tfuru/ConnectedDoll2/shell/image/dist/acrylic_panel_preview.png

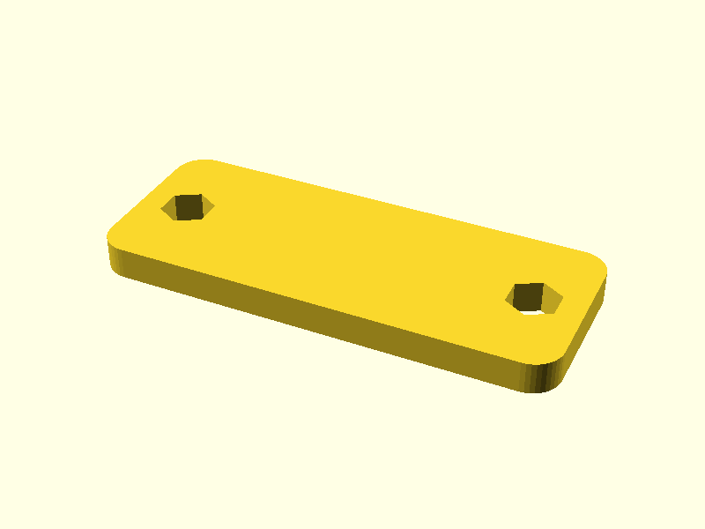
shell/image/dist/acrylic_panel_preview.png
