tfuru/ConnectedDoll2/shell/image/dist/battery_lid_preview.png

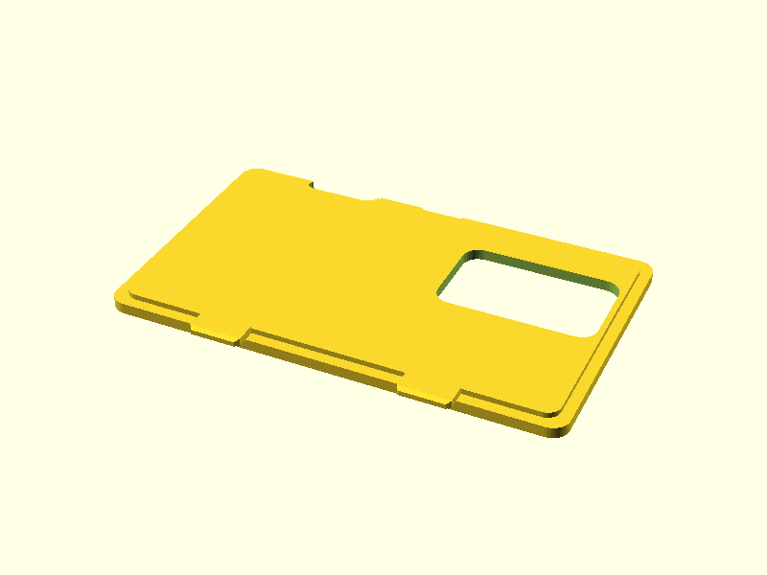
shell/image/dist/battery_lid_preview.png
