tfuru/ConnectedDoll2/shell/image/dist/battery_lid_tab_zoom.png

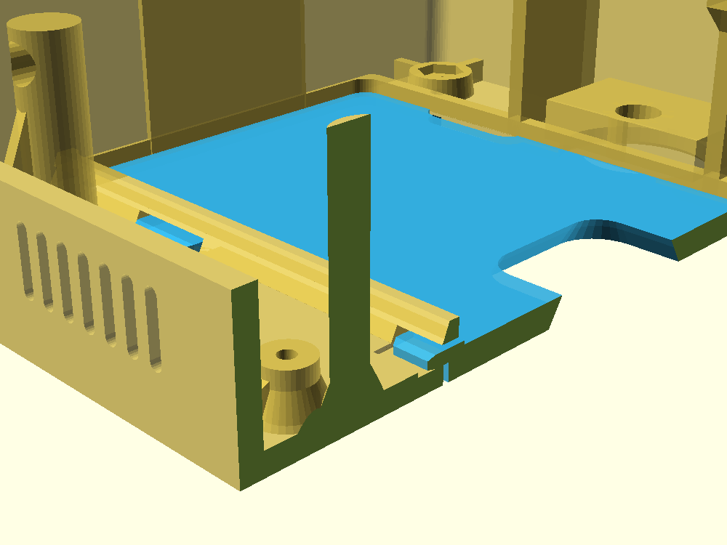
shell/image/dist/battery_lid_tab_zoom.png
