tfuru/ConnectedDoll2/shell/image/dist/bottom_case_preview.png

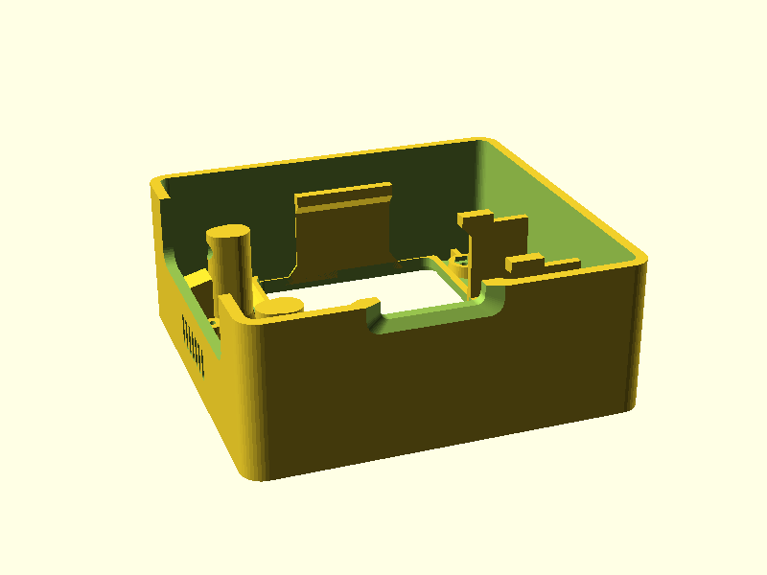
shell/image/dist/bottom_case_preview.png
