tfuru/ConnectedDoll2/shell/image/dist/button_boss_front_zoom.png

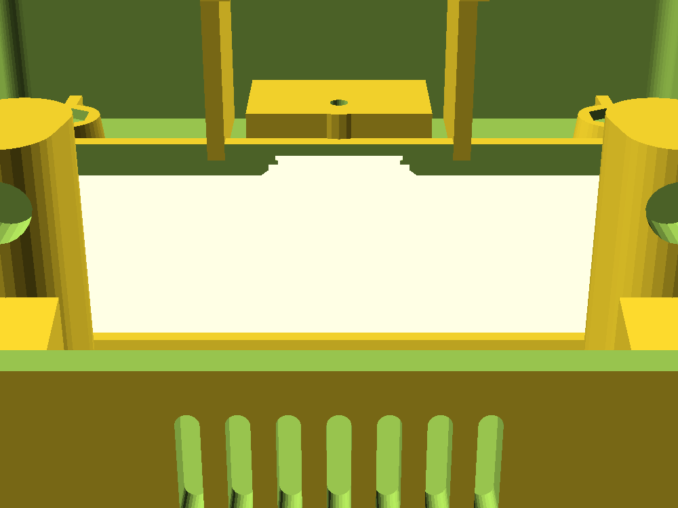
shell/image/dist/button_boss_front_zoom.png
