tfuru/ConnectedDoll2/shell/image/dist/button_boss_zoom.png

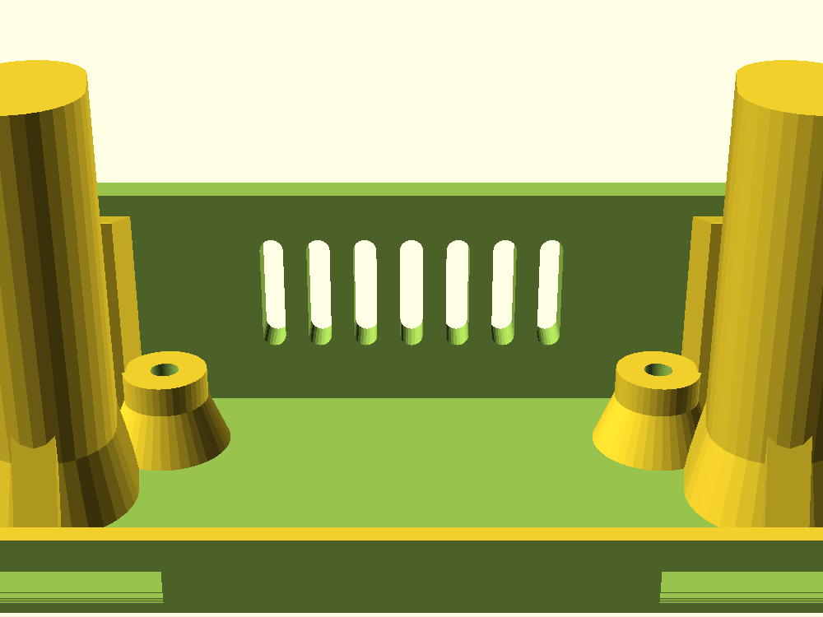
shell/image/dist/button_boss_zoom.png
