tfuru/ConnectedDoll2/shell/image/dist/front_view_preview.png

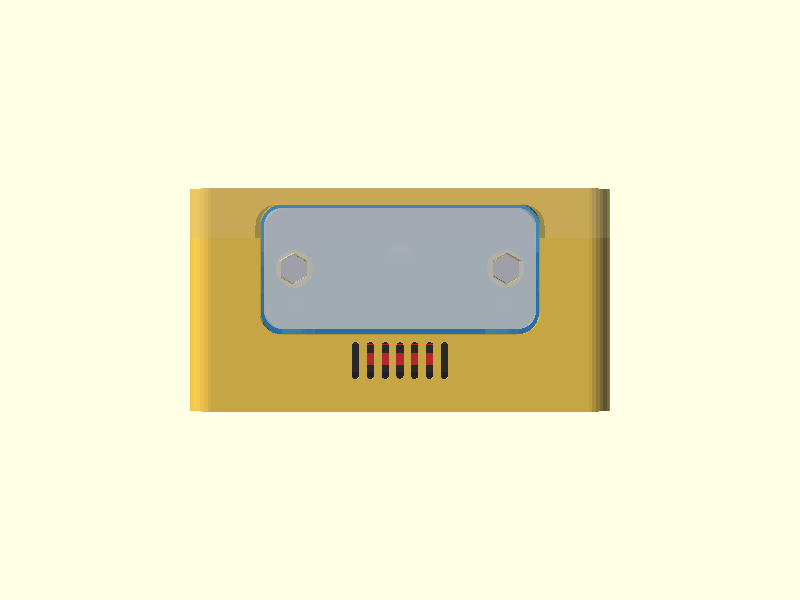
shell/image/dist/front_view_preview.png
