tfuru/ConnectedDoll2/shell/image/dist/rotary_lock_preview.png

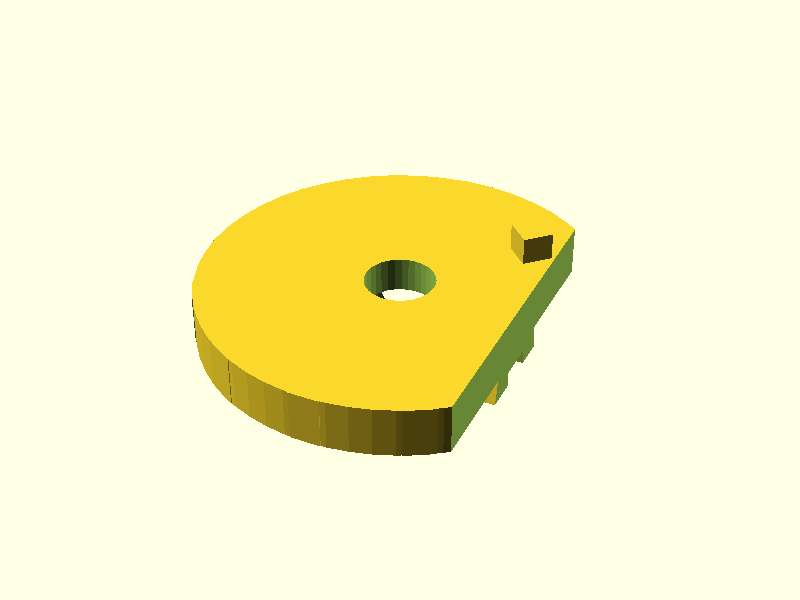
shell/image/dist/rotary_lock_preview.png
