tfuru/ConnectedDoll2/shell/image/dist/rotary_screw_bottom_view.png

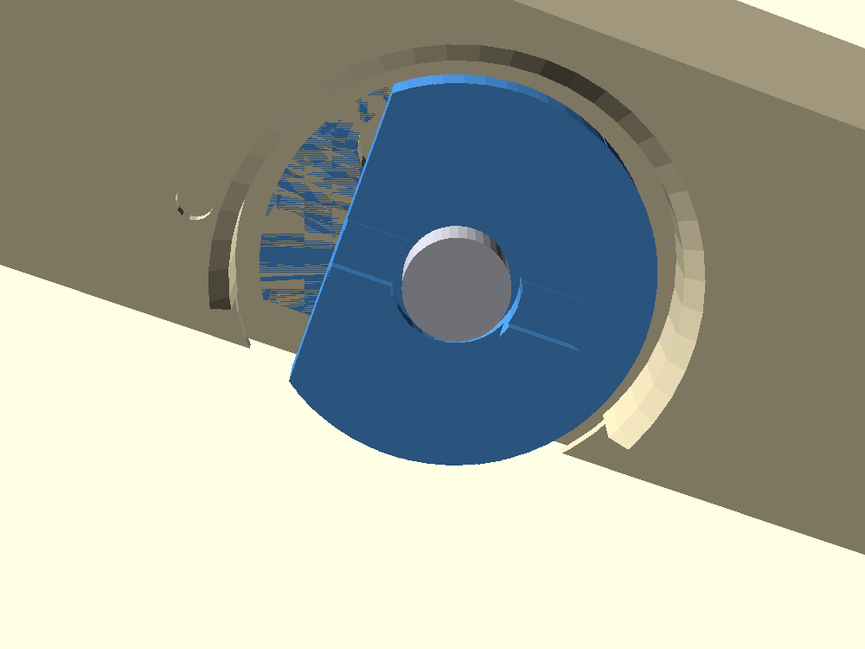
shell/image/dist/rotary_screw_bottom_view.png
