tfuru/ConnectedDoll2/shell/image/dist/rotary_screw_cutaway.png

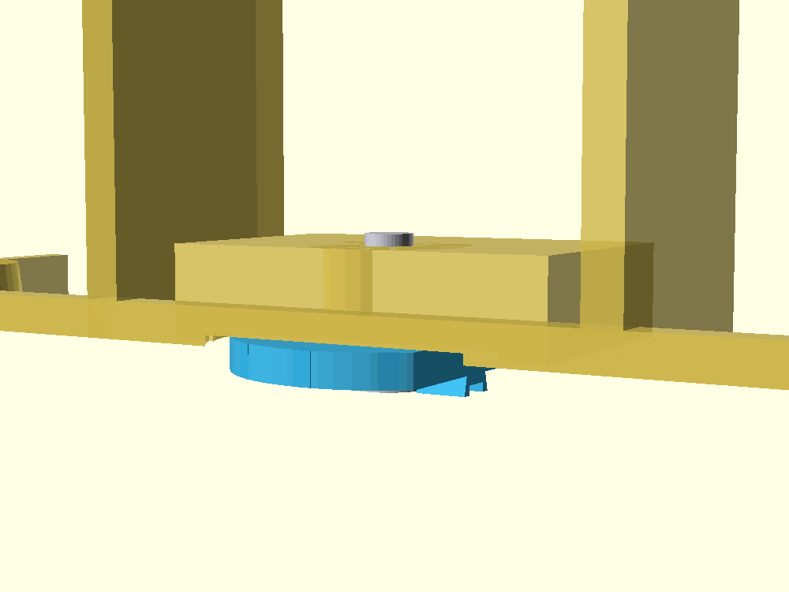
shell/image/dist/rotary_screw_cutaway.png
