tfuru/ConnectedDoll2/shell/image/assembly_front_preview.png

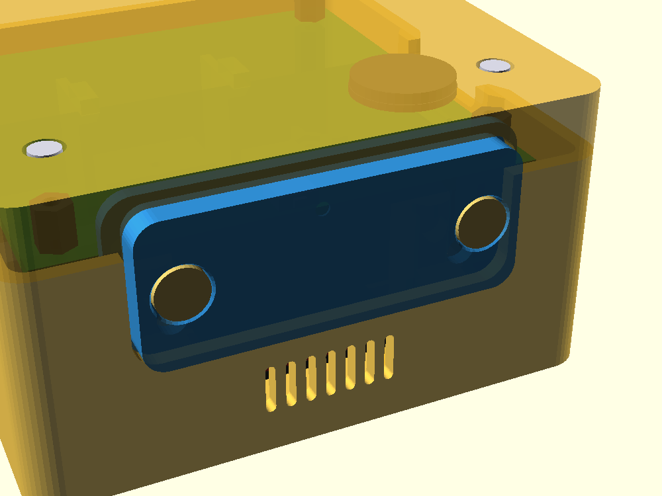
shell/image/assembly_front_preview.png
