tfuru/ConnectedDoll2/shell/image/dist/assembly_bottom_view.png

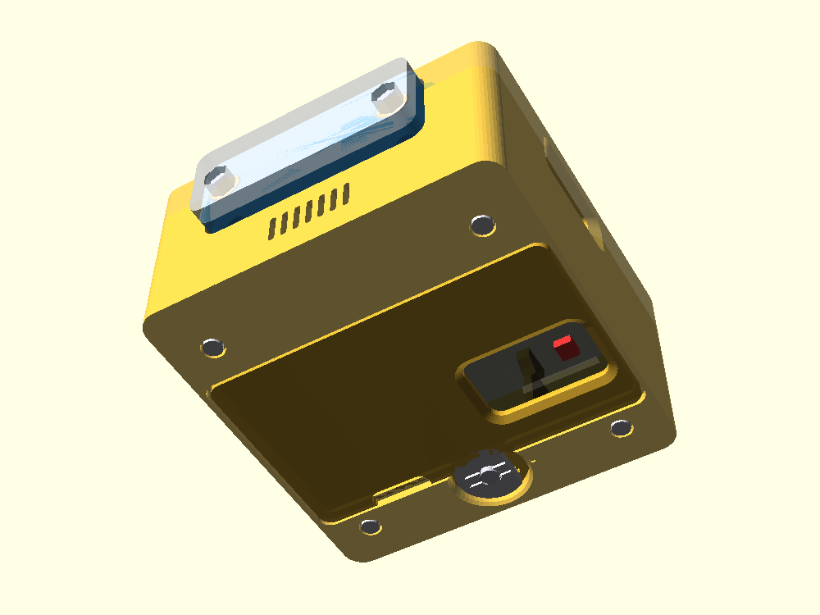
shell/image/dist/assembly_bottom_view.png
