tfuru/ConnectedDoll2/shell/image/dist/assembly_cutaway.png

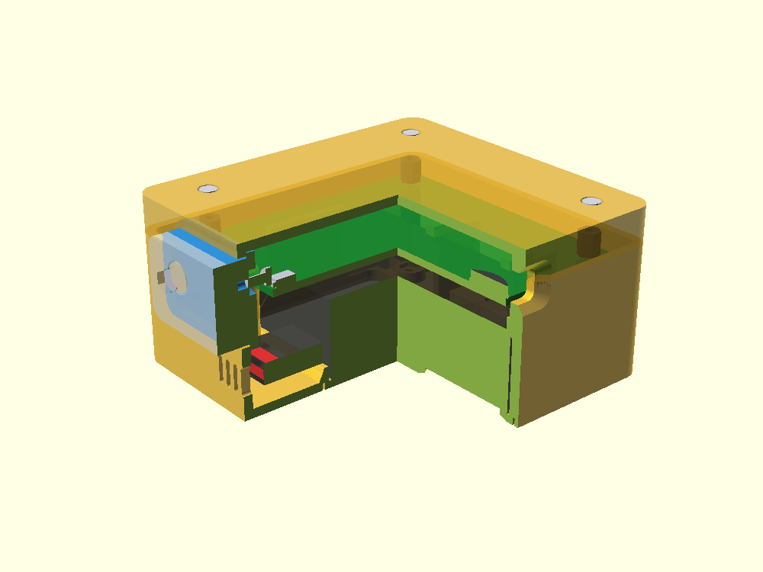
shell/image/dist/assembly_cutaway.png
