tfuru/ConnectedDoll2/shell/image/dist/bottom_lid_installed_view.png

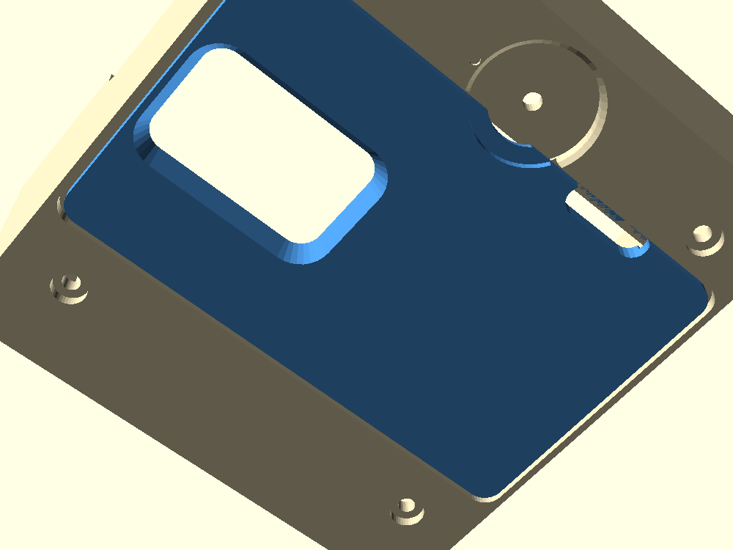
shell/image/dist/bottom_lid_installed_view.png
