tfuru/ConnectedDoll2/shell/image/dist/print_plate_front_inside.png

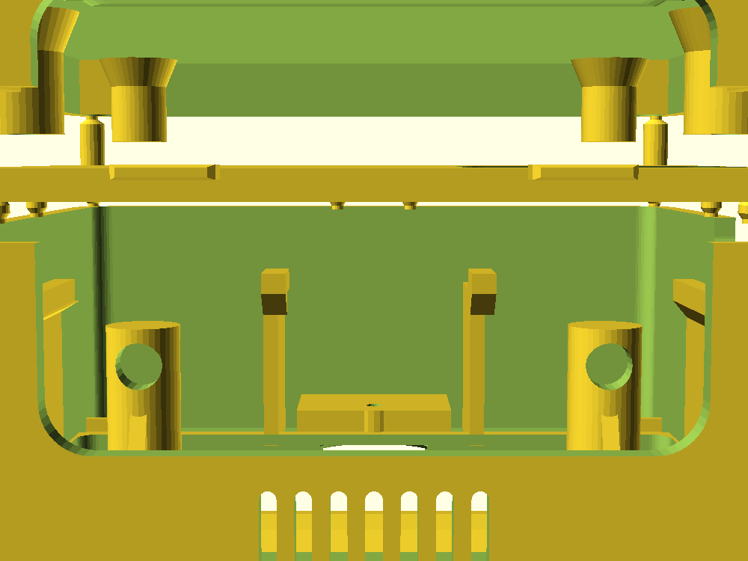
shell/image/dist/print_plate_front_inside.png
