tfuru/ConnectedDoll2/shell/image/dist/print_plate_preview.png

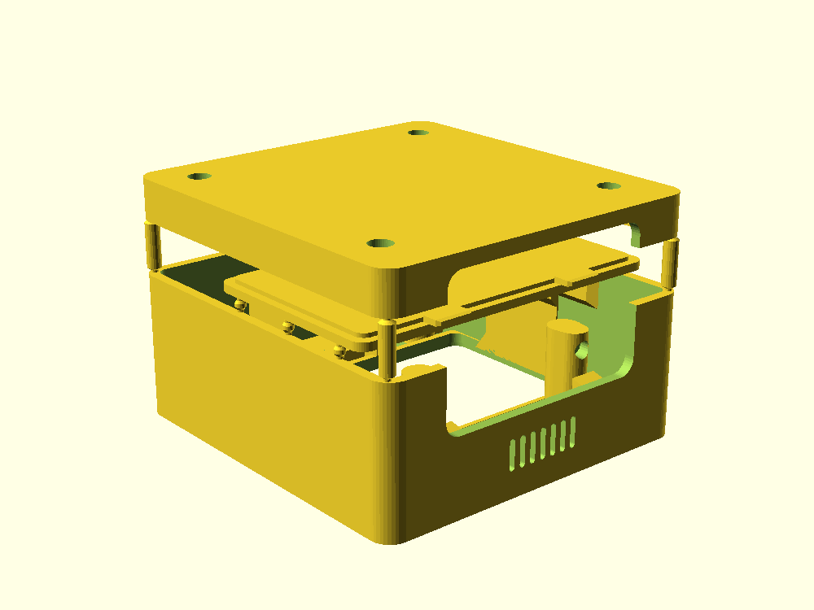
shell/image/dist/print_plate_preview.png
