tfuru/ConnectedDoll2/shell/image/dist/print_plate_rear_view.png

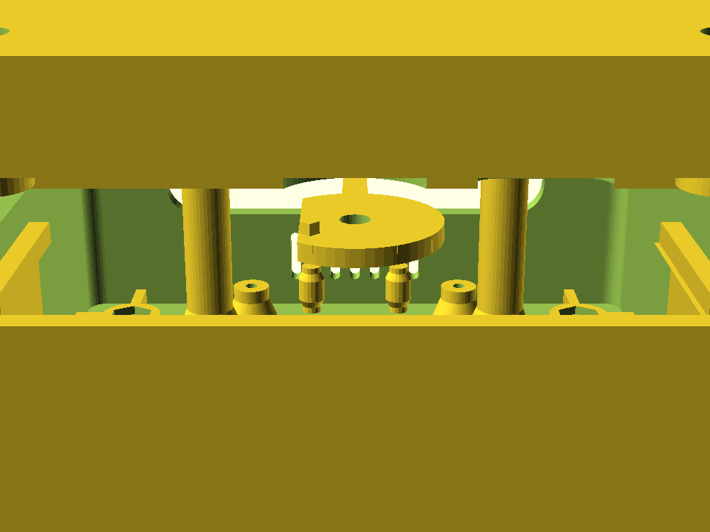
shell/image/dist/print_plate_rear_view.png
